BryggansBryggeri/electrical/relay_sketch/relay_sketch.kicad_pcb

## KiCad design KiCad/lainuri/lainuri.sch

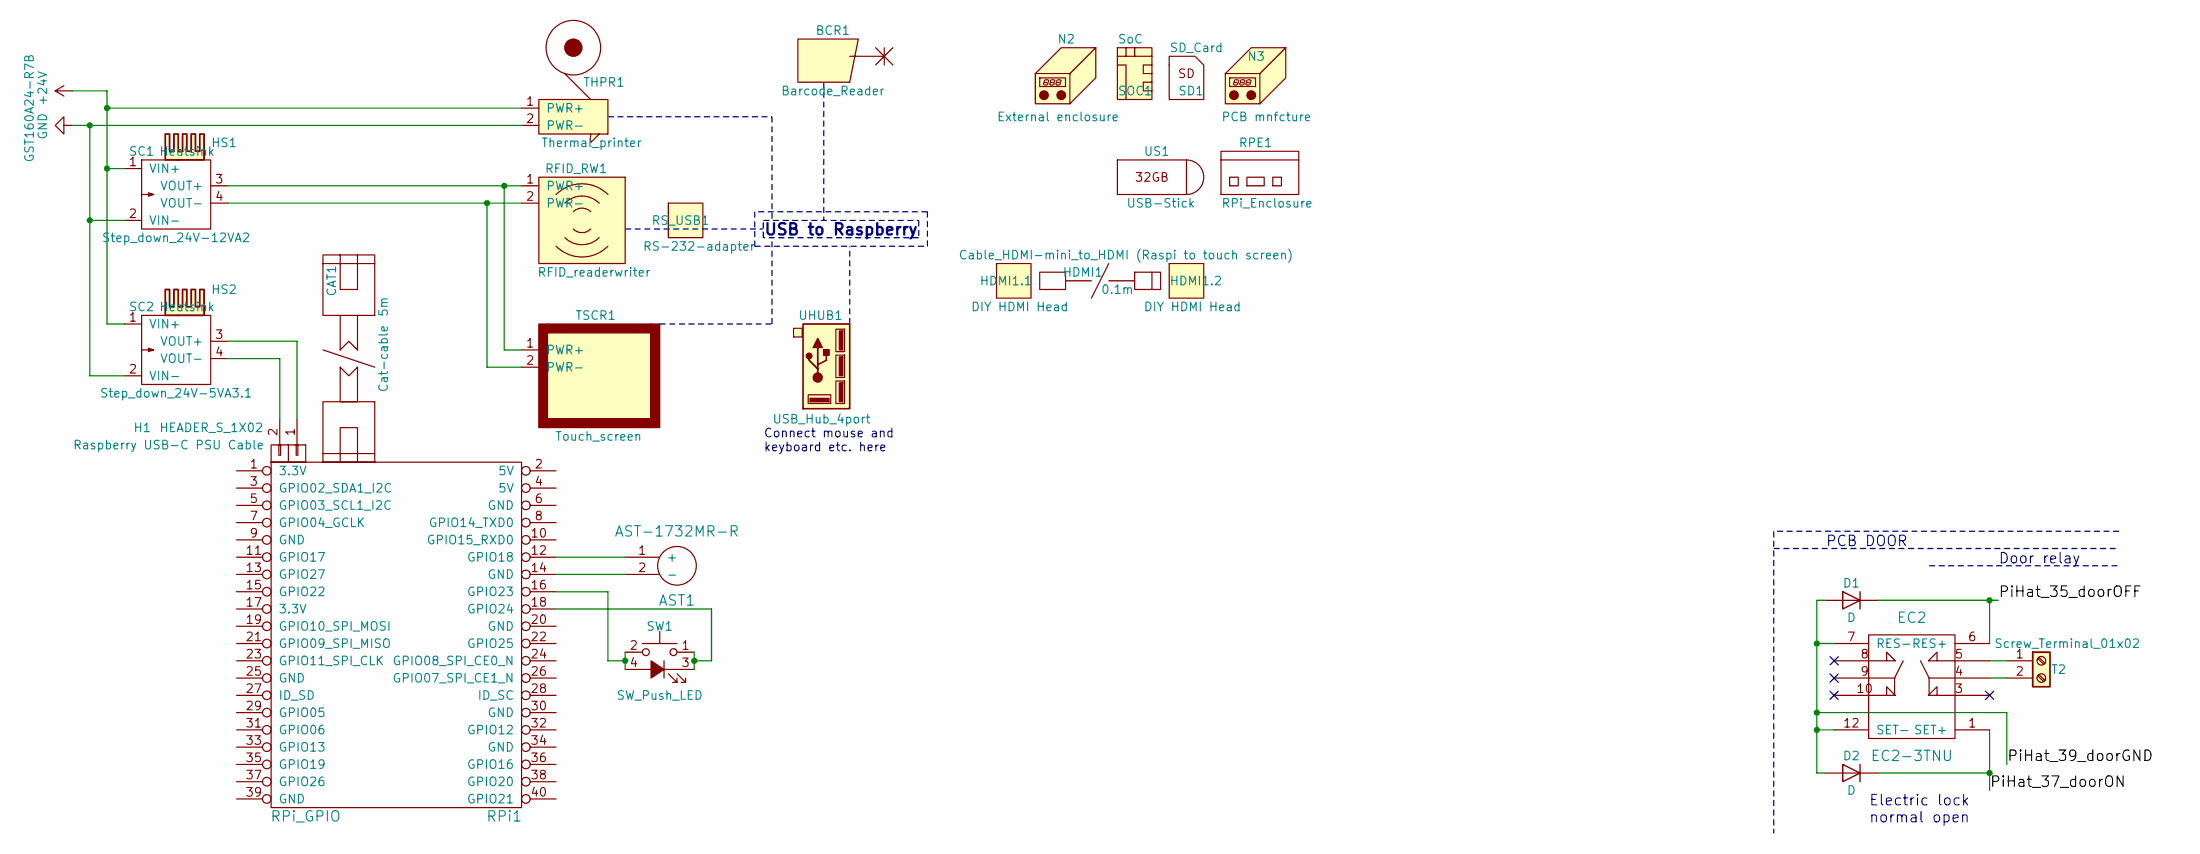
[picture p3: schematic lainuri.sch]

Parts:
AST1: AST-1732MR-R
BCR1: Barcode_Reader
CAT1: Cat-cable; Bad_board_tag
D1, D2: D; 1N4154TAP
EC2: EC2-3TNU
H1: HEADER_S_1X02
HDMI1: Cable_HDMI-mini_to_HDMI (Raspi to touch screen)
HDMI1.1, HDMI1.2: DIY HDMI Head
HS1, HS2: Heatsink
N2: External enclosure
N3: PCB mnfcture
RFID_RW1: RFID_readerwriter
RPE1: RPi_Enclosure; Bad_board_tag
RPi1: RPi_GPIO; PI_GPIO_Header_F_2x20
RS_USB1: RS-232-adapter
SC1: Step_down_24V-12VA2
SC2: Step_down_24V-5VA3.1
SD1: SD_Card; Bad_board_tag
SOC1: SoC; Bad_board_tag
SW1: SW_Push_LED; Molex_KK-6410-04_04x2.54mm_Straight
T2: Screw_Terminal_01x02; Screw_Terminal_01x02 (Molex)
THPR1: Thermal_printer
TSCR1: Touch_screen
UHUB1: USB_Hub_4port
US1: USB-Stick

Connections:
+24V: SC1.1 (VIN+), SC2.1 (VIN+), THPR1.1 (PWR+)
GND: SC1.2 (VIN-), SC2.2 (VIN-), THPR1.2 (PWR-)
unnamed: AST1.1 (+), RPi1.12 (GPIO18)
unnamed: AST1.2 (-), RPi1.14 (GND)
unnamed: EC2.4, T2.2
unnamed: EC2.5, T2.1
unnamed: H1.1, SC2.3 (VOUT+)
unnamed: H1.2, SC2.4 (VOUT-)
unnamed: RFID_RW1.1 (PWR+), SC1.3 (VOUT+), TSCR1.1 (PWR+)
unnamed: RFID_RW1.2 (PWR-), SC1.4 (VOUT-), TSCR1.2 (PWR-)
unnamed: RPi1.16 (GPIO23), SW1.2, SW1.4 (A)
unnamed: RPi1.18 (GPIO24), SW1.1, SW1.3 (K)
PiHat_35_doorOFF: D1.1 (K), EC2.6 (RES+)
PiHat_37_doorON: D2.1 (K), EC2.1 (SET+)
PiHat_39_doorGND: D1.2 (A), D2.2 (A), EC2.7 (RES-), EC2.12 (SET-)

Notes on the sheet:
Door relay
PCB DOOR
Electric lock normal open
USB to Raspberry
Connect mouse and keyboard etc. here
